IvanLi-CN/iso-usb-hub/src/power_in.rs

use defmt::{info, warn};
use embassy_embedded_hal::shared_bus::asynch::i2c::I2cDevice;
use embassy_executor::{task, SpawnError, Spawner};
use embassy_sync::blocking_mutex::raw::CriticalSectionRawMutex;
use embassy_sync::channel::{Channel, Receiver};
use embassy_sync::mutex::Mutex;
use embassy_sync::signal::Signal;
use embassy_time::{Duration, Timer};
use embedded_hal_async::i2c::I2c;
use esp_hal::analog::adc::{Adc, AdcCalLine, AdcPin};
use esp_hal::gpio::{Input, Output};
use esp_hal::peripherals::{ADC1, GPIO4};
use esp_hal::Blocking;
use ina226_tp as ina226;

use crate::boot_diag::{BootFaultCode, SelfCheckItemState};
use crate::power_limits::{classify_voltage, voltage_in_range, VoltageRange};
use crate::I2cBus;

const INA226_ADDR: u8 = 0x44;
// INA226 shunt voltage LSB = 2.5 uV per datasheet and crate constants.
const INA226_SHUNT_LSB_V: f32 = 2.5e-6;
const VIN_ADC_DIVIDER_RATIO: f32 = 11.0;
const RUNTIME_PROTECT_INTERVAL_MS: u64 = 100;
const RUNTIME_STATUS_INTERVAL_TICKS: u16 = 10_000 / RUNTIME_PROTECT_INTERVAL_MS as u16;

pub type InaOp<'a, I2C> = ina226::INA226<&'a mut I2C, ina226::Operational>;
pub type VinAdc = Adc<'static, ADC1<'static>, Blocking>;
pub type VinAdcPin = AdcPin<GPIO4<'static>, ADC1<'static>, AdcCalLine<ADC1<'static>>>;

#[derive(Copy, Clone)]
pub struct Limits {
    pub vin_min_v: f32,
    pub vin_max_v: f32,
    pub idle_current_max_a: f32,
}

impl Default for Limits {
    fn default() -> Self {
        Self {
            vin_min_v: 9.0,
            vin_max_v: 28.0,
            idle_current_max_a: 0.030,
        }
    }
}

#[derive(Copy, Clone, Default)]
pub struct Status {
    pub vin_v: f32,
    pub i_a: f32,
    pub pg_good: bool,
    pub vin_on: bool,
}

#[derive(Copy, Clone)]
pub struct BootstrapStatus {
    pub state: SelfCheckItemState,
    pub fault: BootFaultCode,
    pub vin_v: f32,
    pub pg_good: bool,
    pub ready: bool,
}

static STATUS_CH: Channel<CriticalSectionRawMutex, Status, 8> = Channel::new();
static LATEST_STATUS: Mutex<CriticalSectionRawMutex, Status> = Mutex::new(Status {
    vin_v: 0.0,
    i_a: 0.0,
    pg_good: false,
    vin_on: false,
});
static VIN_ON_SIG: Signal<CriticalSectionRawMutex, bool> = Signal::new();
static BOOTSTRAP_SIG: Signal<CriticalSectionRawMutex, BootstrapStatus> = Signal::new();

fn pin_level_label(is_high: bool) -> &'static str {
    if is_high {
        "high"
    } else {
        "low"
    }
}

fn pg_label(is_good: bool) -> &'static str {
    if is_good {
        "good"
    } else {
        "bad"
    }
}

fn input_switch_label(in_ce_high: bool) -> &'static str {
    if in_ce_high {
        "open"
    } else {
        "closed"
    }
}

fn hold_input_switch_open(in_ce: &mut Output<'_>) {
    // V3 IN_CE drives an NMOS that pulls TPS2490 EN low; high means forced off.
    in_ce.set_high();
}

fn close_input_switch(in_ce: &mut Output<'_>) {
    in_ce.set_low();
}

fn log_input_command(
    phase: &'static str,
    in_ce: &Output<'_>,
    in_pg: &Input<'_>,
    vin_adc_mv: Option<u16>,
) {
    match vin_adc_mv {
        Some(adc_mv) => info!(
            "pwr.in:cmd phase={} in_ce={} switch={} pg={} vin_adc={}mV vin_est={}V",
            phase,
            pin_level_label(in_ce.is_set_high()),
            input_switch_label(in_ce.is_set_high()),
            pg_label(in_pg.is_high()),
            adc_mv,
            adc_mv as f32 / 1000.0 * VIN_ADC_DIVIDER_RATIO
        ),
        None => info!(
            "pwr.in:cmd phase={} in_ce={} switch={} pg={} vin_adc=n/a",
            phase,
            pin_level_label(in_ce.is_set_high()),
            input_switch_label(in_ce.is_set_high()),
            pg_label(in_pg.is_high())
        ),
    }
}

fn read_vin_adc_mv(adc: &mut VinAdc, pin: &mut VinAdcPin) -> Option<u16> {
    nb::block!(adc.read_oneshot(pin)).ok()
}

pub fn status_receiver() -> Receiver<'static, CriticalSectionRawMutex, Status, 8> {
    STATUS_CH.receiver()
}

pub async fn latest_status() -> Status {
    *LATEST_STATUS.lock().await
}

async fn publish_status(status: Status) {
    *LATEST_STATUS.lock().await = status;
    STATUS_CH.send(status).await;
}

#[allow(dead_code)]
pub fn vin_on_signal() -> &'static Signal<CriticalSectionRawMutex, bool> {
    &VIN_ON_SIG
}

pub fn bootstrap_signal() -> &'static Signal<CriticalSectionRawMutex, BootstrapStatus> {
    &BOOTSTRAP_SIG
}

#[allow(clippy::too_many_arguments)]
pub fn spawn(
    spawner: &Spawner,
    bus: &'static Mutex<CriticalSectionRawMutex, I2cBus>,
    in_ce: Output<'static>,
    in_pg: Input<'static>,
    vin_adc: VinAdc,
    vin_adc_pin: VinAdcPin,
    shunt_res_ohms: f32,
    limits: Limits,
) -> Result<(), SpawnError> {
    spawner.spawn(task(
        bus,
        in_ce,
        in_pg,
        vin_adc,
        vin_adc_pin,
        shunt_res_ohms,
        limits,
    ))
}

#[task]
async fn task(
    bus: &'static Mutex<CriticalSectionRawMutex, I2cBus>,
    mut in_ce: Output<'static>,
    in_pg: Input<'static>,
    mut vin_adc: VinAdc,
    mut vin_adc_pin: VinAdcPin,
    shunt_res_ohms: f32,
    limits: Limits,
) {
    // Ensure power path is held open until qualification passes.
    hold_input_switch_open(&mut in_ce);
    log_input_command(
        "hold-open",
        &in_ce,
        &in_pg,
        read_vin_adc_mv(&mut vin_adc, &mut vin_adc_pin),
    );

    let mut i2c = I2cDevice::new(bus);
    let mut dev = ina226::INA226::new(None);
    dev.set_ina_address(INA226_ADDR);
    let mut ina = match dev.initialize(&mut i2c).await {
        Ok(ina) => ina,
        Err(_) => {
            warn!("pwr.in:init failed addr=0x{:02X}", INA226_ADDR);
            BOOTSTRAP_SIG.signal(BootstrapStatus {
                state: SelfCheckItemState::Fatal,
                fault: BootFaultCode::InaUnavailable,
                vin_v: 0.0,
                pg_good: in_pg.is_high(),
                ready: false,
            });
            VIN_ON_SIG.signal(false);
            loop {
                publish_status(Status {
                    vin_v: 0.0,
                    i_a: 0.0,
                    pg_good: in_pg.is_high(),
                    vin_on: false,
                })
                .await;
                Timer::after(Duration::from_secs(10)).await;
            }
        }
    };

    configure_ina(&mut ina, shunt_res_ohms).await;

    let qualified = qualify_startup(&mut ina, shunt_res_ohms, limits).await;
    if !qualified {
        hold_input_switch_open(&mut in_ce);
        log_input_command(
            "qual-failed",
            &in_ce,
            &in_pg,
            read_vin_adc_mv(&mut vin_adc, &mut vin_adc_pin),
        );
        warn!("pwr.in:qual failed; keep switch open");
        let status = sample_status(&mut ina, &in_pg, shunt_res_ohms, limits, false).await;
        BOOTSTRAP_SIG.signal(BootstrapStatus {
            state: SelfCheckItemState::Fatal,
            fault: input_fault(status.vin_v, status.pg_good, limits),
            vin_v: status.vin_v,
            pg_good: status.pg_good,
            ready: false,
        });
        VIN_ON_SIG.signal(false);
        loop {
            publish_status(sample_status(&mut ina, &in_pg, shunt_res_ohms, limits, false).await)
                .await;
            Timer::after(Duration::from_secs(10)).await;
        }
    }

    close_input_switch(&mut in_ce);
    log_input_command(
        "close",
        &in_ce,
        &in_pg,
        read_vin_adc_mv(&mut vin_adc, &mut vin_adc_pin),
    );
    Timer::after(Duration::from_millis(10)).await;
    log_input_command(
        "settle",
        &in_ce,
        &in_pg,
        read_vin_adc_mv(&mut vin_adc, &mut vin_adc_pin),
    );

    let mut vin_on_state = wait_vin_on(&mut ina, &in_pg, limits, 50, 40).await;
    if !vin_on_state.vin_on {
        hold_input_switch_open(&mut in_ce);
        log_input_command(
            "pg-timeout-open",
            &in_ce,
            &in_pg,
            read_vin_adc_mv(&mut vin_adc, &mut vin_adc_pin),
        );
    }
    let bootstrap = if vin_on_state.vin_on {
        BootstrapStatus {
            state: SelfCheckItemState::Ok,
            fault: BootFaultCode::None,
            vin_v: vin_on_state.last_vbus_v,
            pg_good: vin_on_state.last_pg_good,
            ready: true,
        }
    } else {
        BootstrapStatus {
            state: SelfCheckItemState::Fatal,
            fault: input_fault(vin_on_state.last_vbus_v, vin_on_state.last_pg_good, limits),
            vin_v: vin_on_state.last_vbus_v,
            pg_good: vin_on_state.last_pg_good,
            ready: false,
        }
    };
    BOOTSTRAP_SIG.signal(bootstrap);
    VIN_ON_SIG.signal(vin_on_state.vin_on);

    let mut input_switch_open = !vin_on_state.vin_on;
    let mut status_interval_ticks = 0;
    loop {
        let mut status = sample_status(
            &mut ina,
            &in_pg,
            shunt_res_ohms,
            limits,
            vin_on_state.vin_on,
        )
        .await;
        let previous = RuntimeInputState {
            vin_on: vin_on_state.vin_on,
            switch_open: input_switch_open,
        };
        let next = advance_runtime_input_state(previous, status.vin_v, status.pg_good, limits);

        if next.switch_open && !previous.switch_open {
            hold_input_switch_open(&mut in_ce);
            log_input_command(
                "runtime-ovp-open",
                &in_ce,
                &in_pg,
                read_vin_adc_mv(&mut vin_adc, &mut vin_adc_pin),
            );
            warn!("pwr.in:vin_ovp vin={}V; keep switch open", status.vin_v);
        }
        if !next.vin_on && previous.vin_on {
            info!("pwr.in:vin_on=false vin={}V", status.vin_v);
            VIN_ON_SIG.signal(false);
        } else if next.vin_on && !previous.vin_on {
            info!("pwr.in:vin_on=true vin={}V pg=good", status.vin_v);
            VIN_ON_SIG.signal(true);
        }
        vin_on_state.vin_on = next.vin_on;
        input_switch_open = next.switch_open;
        status.vin_on = next.vin_on;

        if next.switch_open != previous.switch_open || status_interval_ticks == 0 {
            info!(
                "pwr.in:stat vin={}V i={}A pg={} vin_on={}",
                status.vin_v,
                status.i_a,
                if status.pg_good { "good" } else { "bad" },
                if status.vin_on { "true" } else { "false" }
            );
            publish_status(status).await;
            status_interval_ticks = RUNTIME_STATUS_INTERVAL_TICKS;
        } else {
            status_interval_ticks -= 1;
        }
        Timer::after(Duration::from_millis(RUNTIME_PROTECT_INTERVAL_MS)).await;
    }
}

async fn sample_status<I2C: I2c>(
    ina: &mut InaOp<'_, I2C>,
    in_pg: &Input<'_>,
    shunt_res_ohms: f32,
    limits: Limits,
    vin_on_state: bool,
) -> Status {
    let vin_v = ina.read_voltage().await as f32;
    let vshunt_v = read_signed_shunt_voltage(ina).await;
    let i_a = vshunt_v / shunt_res_ohms;
    let pg_good = in_pg.is_high();
    let vin_range_ok = voltage_in_range(vin_v, limits.vin_min_v, limits.vin_max_v);

    Status {
        vin_v,
        i_a,
        pg_good,
        vin_on: vin_on_state || (pg_good && vin_range_ok),
    }
}

async fn configure_ina<I2C: I2c>(ina: &mut InaOp<'_, I2C>, shunt_res_ohms: f32) {
    use ina226::{InaAverage, InaMode, InaVbusct, InaVshct};
    ina.set_ina_mode(InaMode::ShuntAndBusContinuous)
        .set_ina_average(InaAverage::_16)
        .set_ina_vbusct(InaVbusct::_1_1_ms)
        .set_ina_vscht(InaVshct::_1_1_ms)
        .commit()
        .await;
    ina.set_ina_calibration(shunt_res_ohms as f64, 10.0f64)
        .commit()
        .await;
}

async fn qualify_startup<I2C: I2c>(
    ina: &mut InaOp<'_, I2C>,
    shunt_res_ohms: f32,
    limits: Limits,
) -> bool {
    let mut ok = false;
    for _ in 0..5 {
        let vbus_v = ina.read_voltage().await as f32;
        let vshunt_v = read_signed_shunt_voltage(ina).await;
        let ishunt_a = vshunt_v / shunt_res_ohms;
        let range_ok = voltage_in_range(vbus_v, limits.vin_min_v, limits.vin_max_v);
        let current_ok = ishunt_a.abs() <= limits.idle_current_max_a;
        info!(
            "pwr.in:qual vbus={}V i={}A range_ok={} current_ok={}",
            vbus_v, ishunt_a, range_ok, current_ok
        );
        if range_ok && current_ok {
            ok = true;
            break;
        }
        Timer::after(Duration::from_millis(20)).await;
    }
    ok
}

#[allow(dead_code)]
struct VinOnResult {
    vin_on: bool,
    last_vbus_v: f32,
    last_pg_good: bool,
}

#[derive(Copy, Clone)]
struct RuntimeInputState {
    vin_on: bool,
    switch_open: bool,
}

fn advance_runtime_input_state(
    state: RuntimeInputState,
    vin_v: f32,
    pg_good: bool,
    limits: Limits,
) -> RuntimeInputState {
    if classify_voltage(vin_v, limits.vin_min_v, limits.vin_max_v) == VoltageRange::Overvoltage {
        RuntimeInputState {
            vin_on: false,
            switch_open: true,
        }
    } else if !state.switch_open
        && !state.vin_on
        && pg_good
        && voltage_in_range(vin_v, limits.vin_min_v, limits.vin_max_v)
    {
        RuntimeInputState {
            vin_on: true,
            switch_open: false,
        }
    } else {
        state
    }
}

async fn wait_vin_on<I2C: I2c>(
    ina: &mut InaOp<'_, I2C>,
    in_pg: &Input<'_>,
    limits: Limits,
    interval_ms: u64,
    max_iters: u32,
) -> VinOnResult {
    let mut vin_on = false;
    let mut last_vbus_v = 0.0f32;
    let mut last_pg_good = false;

    for _ in 0..max_iters {
        let pg_good = in_pg.is_high();
        let vbus_v = ina.read_voltage().await as f32;
        last_vbus_v = vbus_v;
        last_pg_good = pg_good;
        let range_ok = voltage_in_range(vbus_v, limits.vin_min_v, limits.vin_max_v);
        if pg_good && range_ok {
            vin_on = true;
            break;
        }
        Timer::after(Duration::from_millis(interval_ms)).await;
    }

    if vin_on {
        info!("pwr.in:vin_on=true vin={}V pg=good", last_vbus_v);
    } else {
        warn!(
            "pwr.in:vin_on=false vin={}V pg={}",
            last_vbus_v,
            if last_pg_good { "good" } else { "bad" }
        );
    }

    VinOnResult {
        vin_on,
        last_vbus_v,
        last_pg_good,
    }
}

fn input_fault(vin_v: f32, pg_good: bool, limits: Limits) -> BootFaultCode {
    if classify_voltage(vin_v, limits.vin_min_v, limits.vin_max_v) == VoltageRange::Overvoltage {
        BootFaultCode::PowerInOvervoltage
    } else if pg_good {
        BootFaultCode::PowerInUnavailable
    } else {
        BootFaultCode::PowerInPgBad
    }
}

async fn read_signed_shunt_voltage<I2C: I2c>(ina: &mut InaOp<'_, I2C>) -> f32 {
    // INA226 shunt register is a signed 16-bit value (two's complement); convert before scaling.
    let raw = ina.read_raw_shunt_voltage().await;
    let signed = i16::from_be_bytes(raw.to_be_bytes());
    signed as f32 * INA226_SHUNT_LSB_V
}
