IvanLi-CN/iso-usb-hub/src/display/dashboard.rs

// src/display/dashboard.rs
// Dashboard 页面模块

// Keep Rgb565 for colors
use embedded_graphics::pixelcolor::Rgb565;
// Remove other embedded_graphics imports as drawing primitives won't be used directly
use embedded_graphics::prelude::RgbColor;
// Removed: use embedded_graphics::prelude::*; // Unused import
// use embedded_graphics::{
//     mono_font::{ascii::FONT_6X10, MonoTextStyle},
//     prelude::*,
//     text::{Alignment, Text},
//     geometry::Point,
// };

use gc9d01::GC9D01; // Import GC9D01
use crate::display::font::{char_to_mono_bitmap, mono_bitmap_to_rgb565, FONT_8X12_WIDTH, FONT_8X12_HEIGHT}; // Updated constant names

// Import necessary traits for GC9D01 (these are bounds on the GC9D01 struct itself)
use embedded_hal::digital::OutputPin;
use embedded_hal_async::spi::SpiDevice;
use gc9d01::Timer as Gc9d01Timer; // Moved this import up
use core::convert::TryInto; // Added import for try_into
use alloc::format; // Added import for alloc::format!

#[derive(Debug)]
pub enum Error {
    // Add specific error types later if needed
    DriverError, // Placeholder for errors from the GC9D01 driver
    // Add other errors like FontError, LayoutError, etc. as needed
}


// Define colors
const COLOR_VOLTAGE: Rgb565 = Rgb565::YELLOW;
const COLOR_CURRENT: Rgb565 = Rgb565::RED;
const COLOR_POWER: Rgb565 = Rgb565::GREEN;
const COLOR_GRAY: Rgb565 = Rgb565::new(15, 30, 15); // 定义灰色
const COLOR_ORANGE: Rgb565 = Rgb565::new(31, 20, 0); // 定义橙色 (R:31, G:20, B:0)
const COLOR_BLUE: Rgb565 = Rgb565::BLUE; // 定义蓝色

// Dashboard struct, contains data to display
pub struct Dashboard {
    // Data for 3 USB ports: (voltage, current, power)
    port_data: [(f32, f32, f32); 3],
    // Counter for draw calls to control screen clearing frequency
    draw_count: u32,
}

impl Dashboard {
    // Create new Dashboard instance
    pub fn new() -> Self {
        Self {
            port_data: [(0.0, 0.0, 0.0); 3],
            draw_count: 0, // Initialize draw counter
        }
    }

    // Update Dashboard display data for 3 ports: [(V1, A1, W1), (V2, A2, W2), (V3, A3, W3)]
    pub fn update_data(&mut self, data: [(f32, f32, f32); 3]) {
        self.port_data = data;
    }

    // Draw Dashboard directly to the display driver using write_area
    // Accept GC9D01 directly
    pub async fn draw<'a, BUS, DC, RST, TIMER>(&mut self, display: &mut GC9D01<'a, BUS, DC, RST, TIMER>) -> Result<(), Error>
    where
        BUS: SpiDevice,
        DC: OutputPin<Error = core::convert::Infallible>, // Specify Infallible error type
        RST: OutputPin<Error = core::convert::Infallible>, // Specify Infallible error type
        TIMER: Gc9d01Timer,
    {
        // Clear screen manually by writing black pixels to the whole area
        let screen_width = 160; // Assuming landscape 160x40
        let screen_height = 40;
        let _black_pixel = Rgb565::BLUE;
        // Create a buffer for a 20x20 block of black pixels
        // const BLOCK_SIZE: u16 = 20; // Removed unused constant

        // Clear screen manually by writing black pixels to the whole area
        // Only clear every 1000 draws to save resources
        if self.draw_count % 1000 == 0 {
            let _ = display.fill_color(Rgb565::BLACK).await;
            // Handle potential remaining rows/columns if screen dimensions are not multiples of BLOCK_SIZE
            // (Assuming 160x40 is a multiple of 20x20, so no extra handling needed for this specific case)
        }
        self.draw_count += 1;
        // (Assuming 160x40 is a multiple of 20x20, so no extra handling needed for this specific case)


        // Layout: 3 columns, 2 rows
        let col_width = screen_width / 3; // Approx 53
        let _row_height = screen_height / 3; // Approx 13 // Mark as unused
        let row_spacing = 1; // Additional spacing between rows
        let actual_row_height = FONT_8X12_HEIGHT + row_spacing; // 12 + 1 = 13

        // Buffer for character pixels (8x12)
        let mut char_pixel_buffer = [Rgb565::BLACK; FONT_8X12_WIDTH * FONT_8X12_HEIGHT]; // Updated constant names

        // Helper function to draw a string
        // Helper function to draw a string with right alignment
        async fn draw_string<'a, BUS, DC, RST, TIMER>(
            display: &mut GC9D01<'a, BUS, DC, RST, TIMER>,
            s: &str,
            right_edge_x: usize, // Right edge of the drawing area
            start_y: usize,
            fg_color: Rgb565,
            bg_color: Rgb565,
            char_pixel_buffer: &mut [Rgb565], // Pass buffer as argument
        ) -> Result<(), Error>
        where
            BUS: SpiDevice,
            DC: OutputPin<Error = core::convert::Infallible>, // Specify Infallible error type
            RST: OutputPin<Error = core::convert::Infallible>, // Specify Infallible error type
            TIMER: Gc9d01Timer,
        {
            let string_pixel_width = s.chars().count() * FONT_8X12_WIDTH;
            let start_x = right_edge_x.saturating_sub(string_pixel_width); // Calculate start_x for right alignment, handle potential underflow

            let mut current_x = start_x;
            for c in s.chars() {
                if let Some(bitmap) = char_to_mono_bitmap(c) {
                    mono_bitmap_to_rgb565(bitmap, fg_color, bg_color, char_pixel_buffer);

                    let x0 = current_x;
                    let y0 = start_y;
                    let _x1 = x0 + FONT_8X12_WIDTH - 1; // Updated constant name
                    let _y1 = y0 + FONT_8X12_HEIGHT - 1; // Updated constant name

                    display.write_area(
                        x0.try_into().unwrap(),
                        y0.try_into().unwrap(),
                        FONT_8X12_WIDTH.try_into().unwrap(), // Updated constant name
                        FONT_8X12_HEIGHT.try_into().unwrap(), // Updated constant name
                        char_pixel_buffer,
                    ).await.map_err(|_| Error::DriverError)?;

                    current_x += FONT_8X12_WIDTH; // Updated constant name
                } else {
                    // Handle characters not in font (e.g., draw a blank space)
                    current_x += FONT_8X12_WIDTH; // Updated constant name // Just advance cursor for now
                }
            }
            Ok(())
        }

        // Draw values
        let mut buffer: [u8; 10] = [0; 10]; // Buffer for float to string conversion

        // Draw data for each port (column)
        for i in 0..3 {
            let _col_start_x = i * col_width; // Mark as unused
            let col_right_edge_x = (i + 1) * col_width;

            let port_voltage = self.port_data[i].0;
            let port_current = self.port_data[i].1;
            let port_power = self.port_data[i].2;

            // Determine Voltage color
            let voltage_color = if port_voltage > 6.0 {
                COLOR_ORANGE
            } else if port_voltage > 2.0 {
                COLOR_VOLTAGE // Yellow
            } else {
                COLOR_GRAY
            };

            // Determine Current and Power colors based on Power
            let (current_color, power_color) = if port_power < 0.05 {
                (COLOR_GRAY, COLOR_GRAY)
            } else {
                let p_color = if port_power > 5.0 {
                    COLOR_BLUE
                } else {
                    COLOR_POWER // Green
                };
                (COLOR_CURRENT, p_color) // Red for current
            };


            // Draw Voltage (Row 1)
            let voltage_str = self.float_to_string(&mut buffer, port_voltage);
            draw_string(display, &format!("{}V", voltage_str), col_right_edge_x as usize, 0, voltage_color, Rgb565::BLACK, &mut char_pixel_buffer).await?;

            // Draw Current (Row 2)
            let current_str = self.float_to_string(&mut buffer, port_current);
            draw_string(display, &format!("{}A", current_str), col_right_edge_x as usize, actual_row_height as usize, current_color, Rgb565::BLACK, &mut char_pixel_buffer).await?;

            // Draw Power (Row 3)
            let power_str = self.float_to_string(&mut buffer, port_power);
            draw_string(display, &format!("{}W", power_str), col_right_edge_x as usize, (actual_row_height * 2) as usize, power_color, Rgb565::BLACK, &mut char_pixel_buffer).await?;
        }

        Ok(())
    }

    // Simplified float to string function (moved from inside draw)
    fn float_to_string<'a>(&self, buffer: &'a mut [u8], value: f32) -> &'a str { // Added &self and value parameter and lifetime
        // This is a very simplified implementation for demonstration only
        // Does not handle negative numbers, large numbers, or specific precision well
        let integer_part = value as i32;
        let decimal_part = ((value - integer_part as f32).abs() * 100.0) as i32; // Get two decimal places, handle negative input

        let mut cursor = 0;
        if value < 0.0 {
            buffer[cursor] = b'-';
            cursor += 1;
        }
        let mut temp = integer_part.abs();
        let mut divisor = 1;
        while divisor * 10 <= temp {
            divisor *= 10;
        }
        while divisor > 0 {
            buffer[cursor] = b'0' + (temp / divisor) as u8;
            cursor += 1;
            temp %= divisor;
            divisor /= 10;
        }
         if integer_part == 0 && value.abs() < 1.0 && value >= 0.0 { // Handle 0.x case
             buffer[cursor] = b'0';
             cursor += 1;
        } else if integer_part == 0 && value.abs() < 1.0 && value < 0.0 && cursor == 1 { // Handle -0.x case
             buffer[cursor] = b'0';
             cursor += 1;
        }


        buffer[cursor] = b'.';
        cursor += 1;

        buffer[cursor] = b'0' + (decimal_part / 10) as u8;
        cursor += 1;
        buffer[cursor] = b'0' + (decimal_part % 10) as u8;
        cursor += 1;

        core::str::from_utf8(&buffer[..cursor]).unwrap_or("Err")
    }
}
